joeferner/raspberry-pi-ir-hat/src/ioctl.rs

use anyhow::Result;
use nix::convert_ioctl_res;
use nix::libc::ioctl;
use std::os::fd::RawFd;

#[cfg(target_pointer_width = "64")]
pub fn write_u32(fd: RawFd, cmd: u32, data: u32) -> Result<i32> {
    let data_bytes = data.to_le_bytes();
    let ret = convert_ioctl_res!(unsafe { ioctl(fd, cmd as u64, data_bytes.as_ptr()) })?;
    Ok(ret)
}

#[cfg(target_pointer_width = "32")]
pub fn write_u32(fd: RawFd, cmd: u32, data: u32) -> Result<i32> {
    let data_bytes = data.to_le_bytes();
    let ret = convert_ioctl_res!(unsafe { ioctl(fd, cmd, data_bytes.as_ptr()) })?;
    Ok(ret)
}
